rev-enge/atlas-copco/1089935597/schematic/1089935597/1089935597.kicad_sch

## KiCad design 1089935597/schematic/1089935597/1089935597.kicad_sch (2024-10-22, an earlier design)

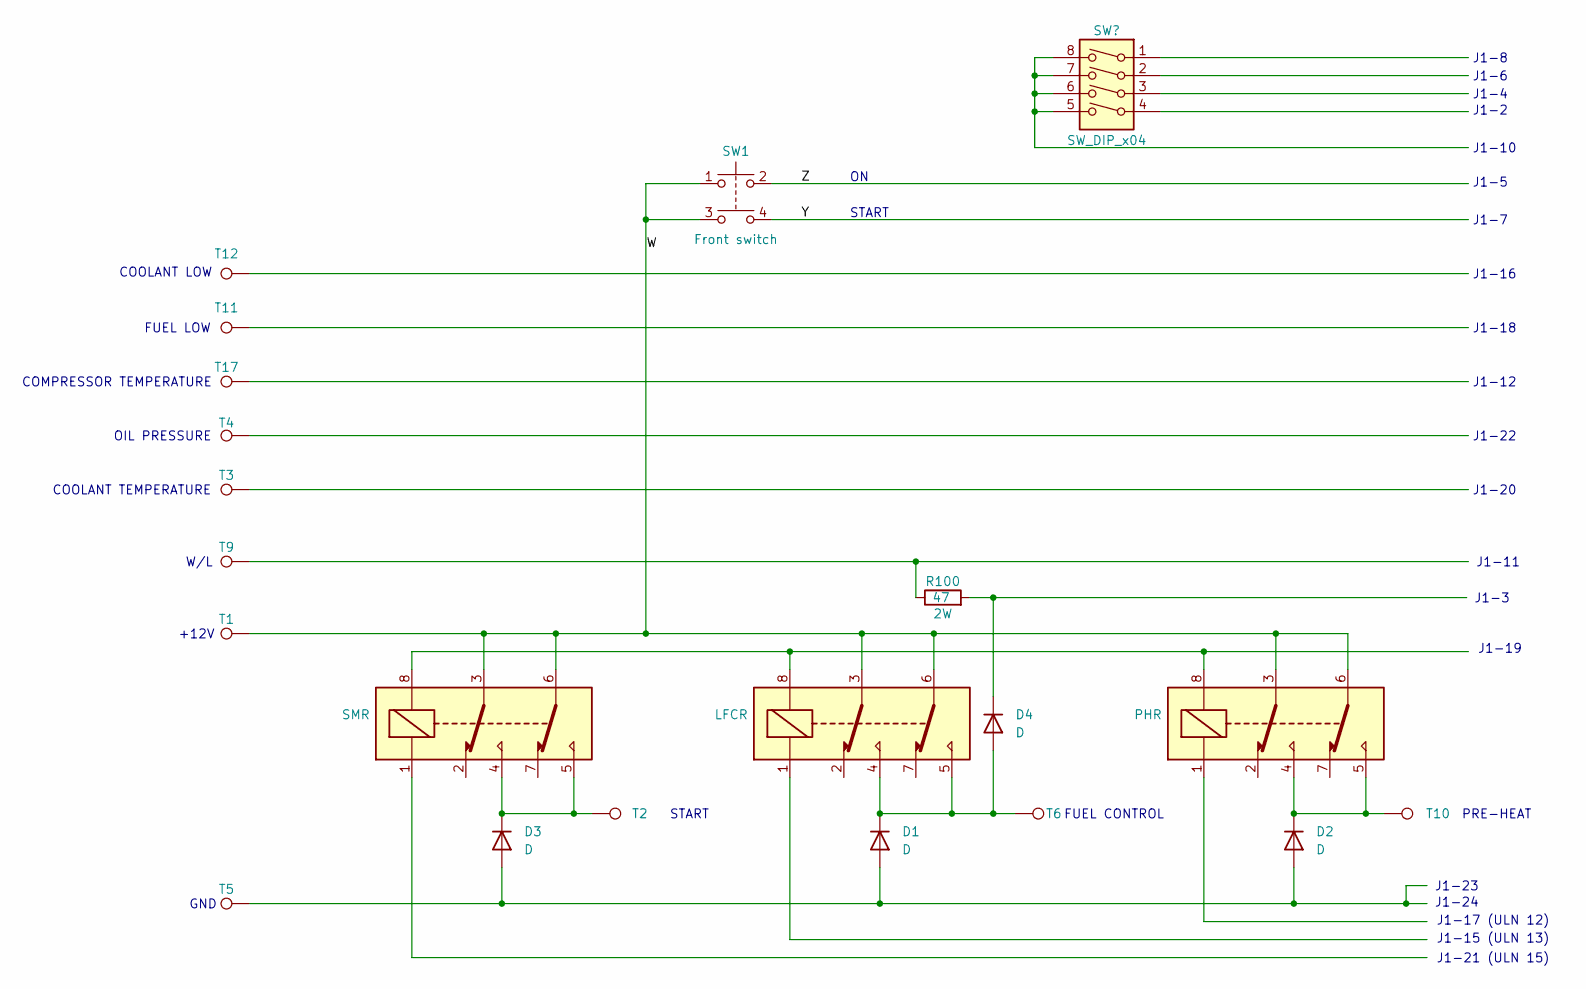
[picture p4: schematic 1089935597.kicad_sch]

Parts:
D1, D2, D3, D4: D
LFCR: G2RL-2-DC12; Relay_DPDT_Omron_G2RL
PHR: G2RL-2-DC12; Relay_DPDT_Omron_G2RL
R100: 47
SMR: G2RL-2-DC12; Relay_DPDT_Omron_G2RL
SW1: Front switch
T1, T2, T3, T4, T5, T6, T9, T10, T11, T12, T17: TestPoint

Connections:
unnamed: D1.1 (K), D4.2 (A), LFCR.4, LFCR.5, T6.1
unnamed: D1.2 (A), D2.2 (A), D3.2 (A), T5.1
unnamed: D2.1 (K), PHR.4, PHR.5, T10.1
unnamed: D3.1 (K), SMR.4, SMR.5, T2.1
unnamed: D4.1 (K), R100.2
unnamed: LFCR.8, PHR.8, SMR.8
unnamed: R100.1, T9.1
W: LFCR.3, LFCR.6, PHR.3, PHR.6, SMR.3, SMR.6, SW1.1, SW1.3, T1.1
Y: SW1.4
Z: SW1.2

Notes on the sheet:
J1-15 (ULN 13)
J1-11
J1-5
J1-4
J1-20
START
J1-16
J1-3
J1-21 (ULN 15)
J1-17 (ULN 12)
COOLANT LOW
COMPRESSOR TEMPERATURE
J1-18
J1-8
J1-12
J1-22
J1-6
J1-10
GND
+12V
FUEL CONTROL
W/L
PRE-HEAT
J1-7
J1-23
J1-2
FUEL LOW
J1-24
OIL PRESSURE
COOLANT TEMPERATURE
J1-19
