rev-enge/atlas-copco/1089935597/schematic/1089935597/cpu.kicad_sch

## KiCad design 1089935597/schematic/1089935597/cpu.kicad_sch (2024-10-22, an earlier design)

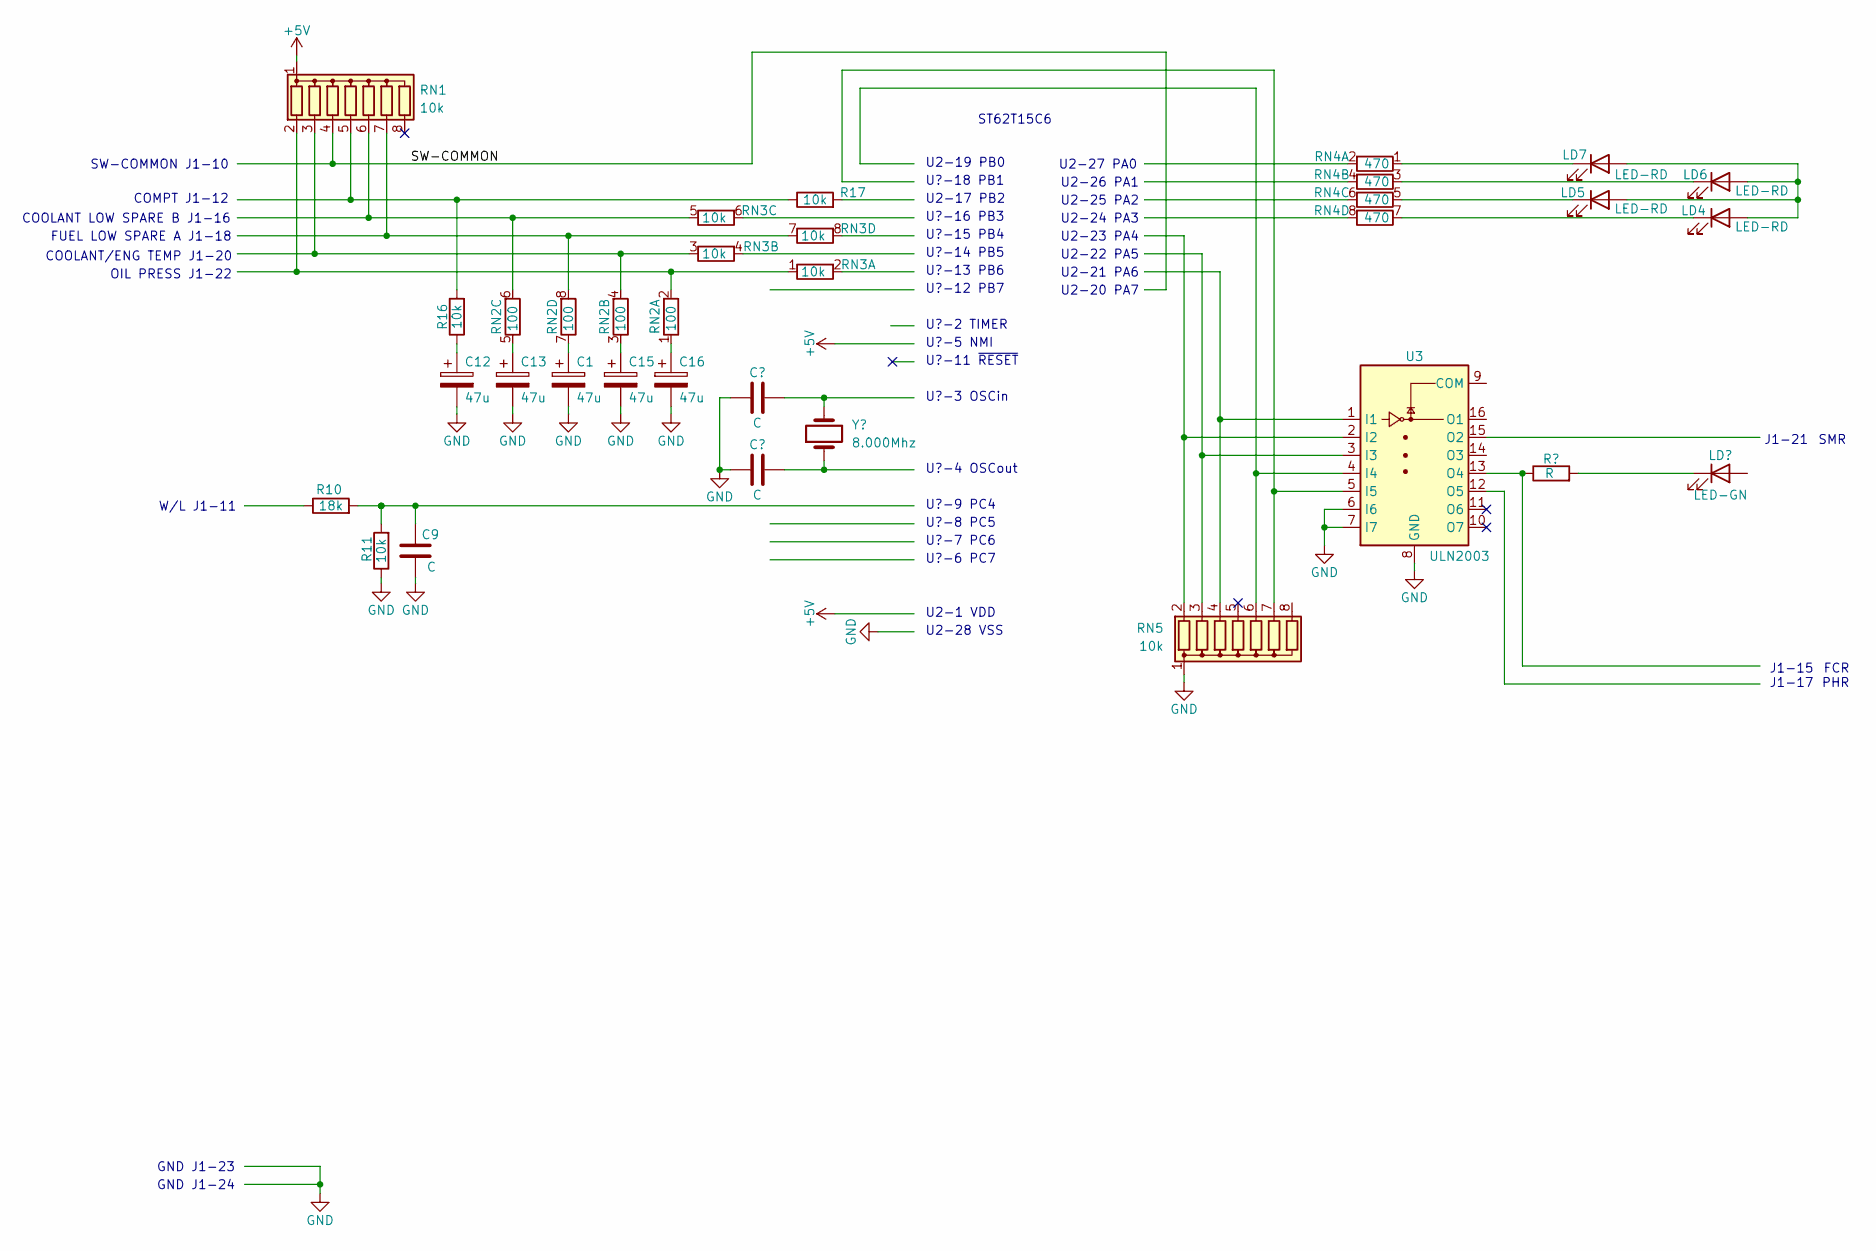
[picture p5: schematic cpu.kicad_sch]

Parts:
C1, C12, C13, C15, C16: 47u
C9: C
LD4, LD5, LD6, LD7: LED-RD
R10: 18k
R11, R16, R17: 10k
RN1, RN3, RN5: 10k; R_Array_SIP8
RN2: 100; R_Array_SIP8
RN4: 470; R_Array_SIP8
U3: ULN2003

Connections:
unnamed: C1.1, RN2.7 (R4.1)
unnamed: C9.1, R10.2
unnamed: C12.1, R16.1
unnamed: C13.1, RN2.5 (R3.1)
unnamed: C15.1, RN2.3 (R2.1)
unnamed: C16.1, RN2.1 (R1.1)
unnamed: LD4.1 (K), RN4.7 (R4.1)
unnamed: LD4.2 (A), LD5.2 (A), LD6.2 (A), LD7.2 (A)
unnamed: LD5.1 (K), RN4.5 (R3.1)
unnamed: LD6.1 (K), RN4.3 (R2.1)
unnamed: LD7.1 (K), RN4.1 (R1.1)
unnamed: R16.2, R17.1, RN1.5 (R4)
unnamed: RN1.2 (R1), RN2.2 (R1.2), RN3.1 (R1.1)
unnamed: RN1.3 (R2), RN2.4 (R2.2), RN3.3 (R2.1)
unnamed: RN1.6 (R5), RN2.6 (R3.2), RN3.5 (R3.1)
unnamed: RN1.7 (R6), RN2.8 (R4.2), RN3.7 (R4.1)
unnamed: RN5.2 (R1), U3.2 (I2)
unnamed: RN5.3 (R2), U3.3 (I3)
unnamed: RN5.4 (R3), U3.1 (I1)
unnamed: RN5.6 (R5), U3.4 (I4)
unnamed: RN5.7 (R6), U3.5 (I5)
unnamed: U3.6 (I6), U3.7 (I7)
SW-COMMON: RN1.4 (R3)

Notes on the sheet:
U?-4 OSCout
U2-23 PA4
U2-20 PA7
U2-27 PA0
COOLANT LOW SPARE B J1-16
U2-17 PB2
U?-13 PB6
U?-6 PC7
ST62T15C6
W/L J1-11
J1-21
U?-7 PC6
U?-11 ~{RESET}
U2-24 PA3
U2-21 PA6
U2-26 PA1
U?-16 PB3
J1-15
SW-COMMON J1-10
U2-28 VSS
FCR
U?-14 PB5
U?-2 TIMER
SMR
U2-1 VDD
U2-22 PA5
U?-3 OSCin
GND J1-24
U?-9 PC4
COMPT J1-12
U?-12 PB7
U2-19 PB0
PHR
COOLANT/ENG TEMP J1-20
U?-5 NMI
U2-25 PA2
J1-17
GND J1-23
U?-18 PB1
U?-8 PC5
U?-15 PB4
OIL PRESS J1-22
FUEL LOW SPARE A J1-18
